Juno-cyber/Xiaotian_Epaper/4.CAD_Model/texture/封面2.jpg

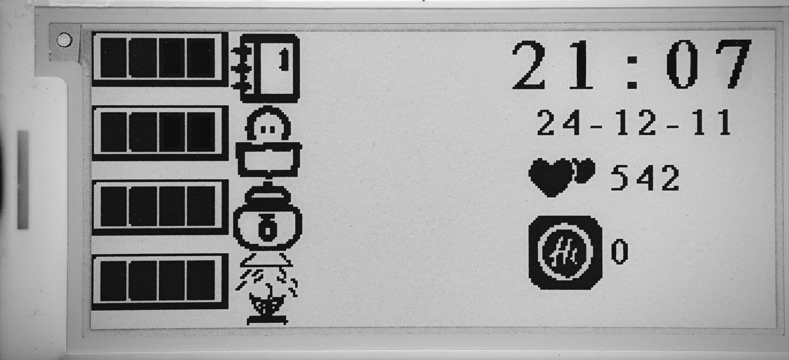
4.CAD_Model/texture/封面2.jpg
