Juno-cyber/Xiaotian_Epaper/7.img/展示图/keyshot.10.jpg

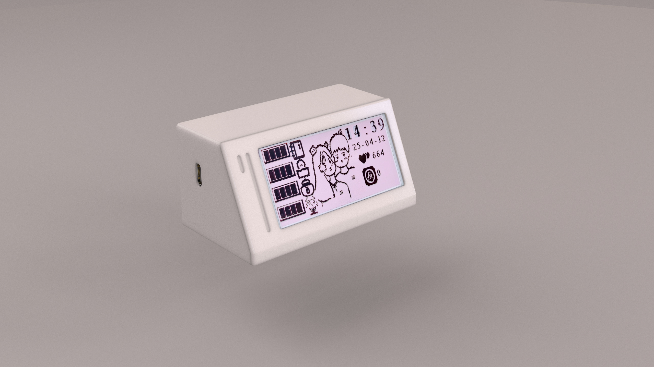
7.img/展示图/keyshot.10.jpg
