Juno-cyber/Xiaotian_Epaper/7.img/展示图/xiaotian3.jpg

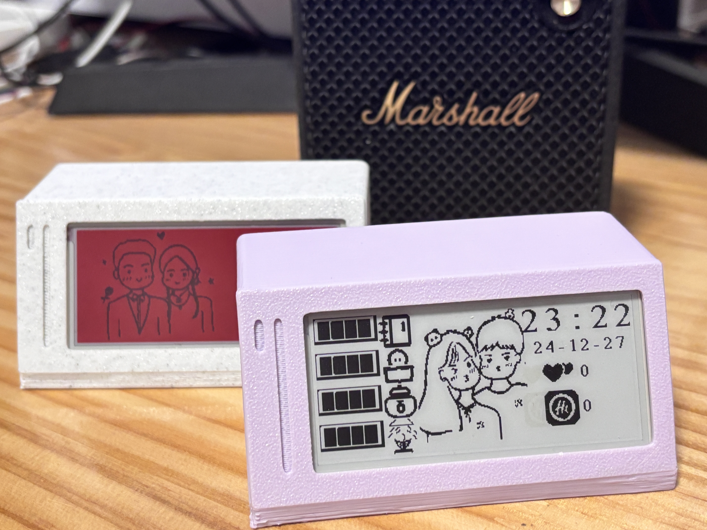
7.img/展示图/xiaotian3.jpg
