Juno-cyber/Xiaotian_Epaper/7.img/展示图/xiaotian5.jpg

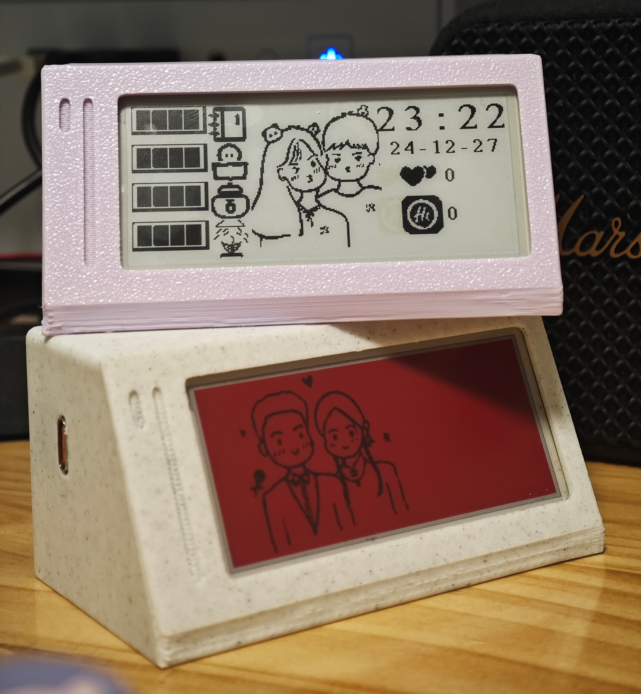
7.img/展示图/xiaotian5.jpg
