Juno-cyber/Xiaotian_Epaper/7.img/展示图/微信图片_20250413101004.jpg

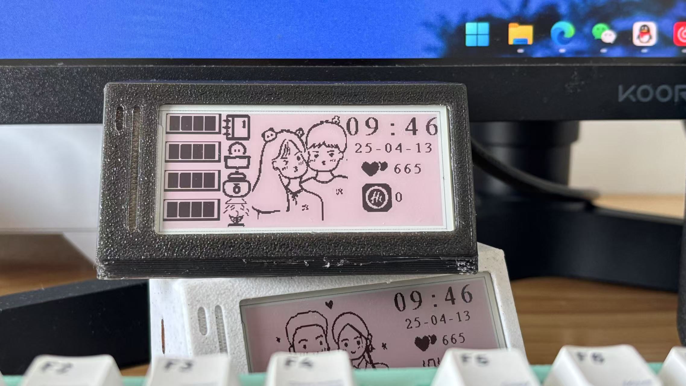
7.img/展示图/微信图片_20250413101004.jpg
